janelia-kicad/LED-Display_G4_Hardware_Arena/docs/assets/arena_12-12_v2_back_iso-render.png

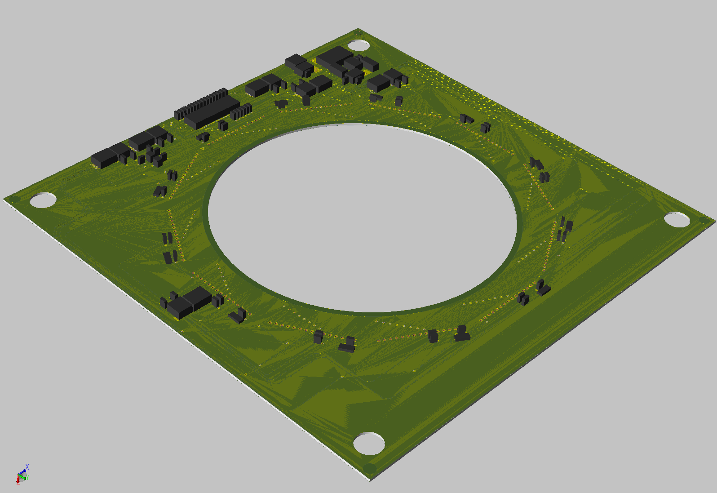
docs/assets/arena_12-12_v2_back_iso-render.png
