janelia-kicad/LED-Display_G4_Hardware_Arena/docs/assets/arena_12-12_v6p0_front_iso-render.png

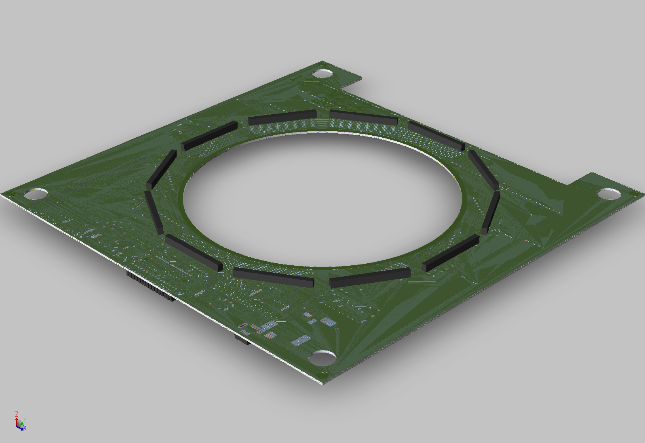
docs/assets/arena_12-12_v6p0_front_iso-render.png
