janelia-kicad/LED-Display_G4_Hardware_Arena/docs/assets/g4_with-placeholder_iso-photo.jpg

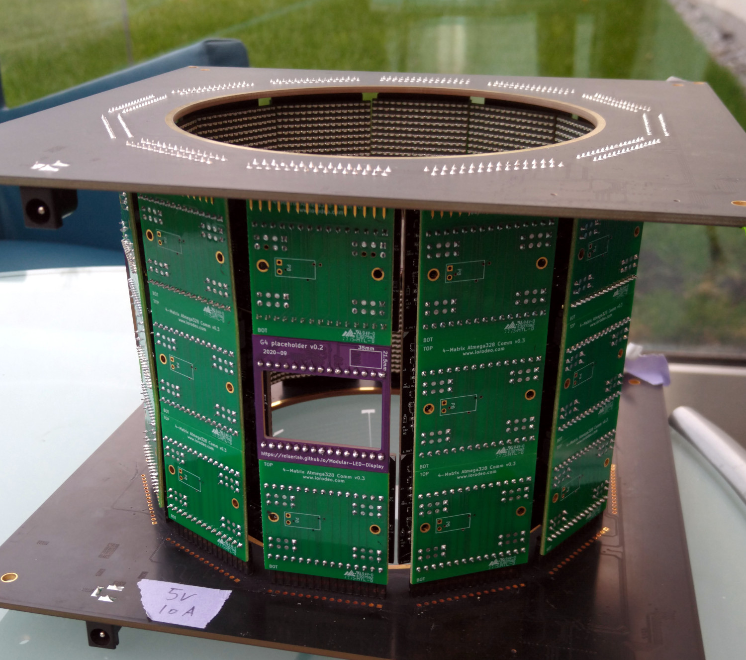
docs/assets/g4_with-placeholder_iso-photo.jpg
