janelia-kicad/LED-Display_G4_Hardware_Arena/docs/assets/g4_with-placeholder_photo.jpg

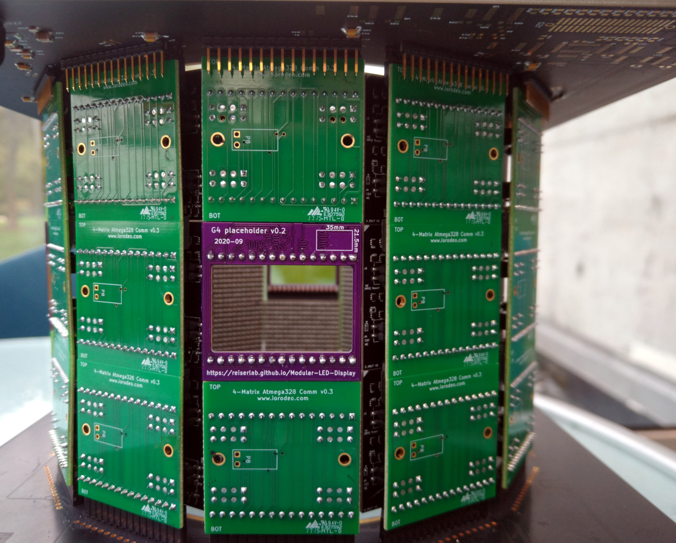
docs/assets/g4_with-placeholder_photo.jpg
