janelia-kicad/LED-Display_G4_Hardware_Arena/docs/assets/interconnect_v1_front_photo.jpg

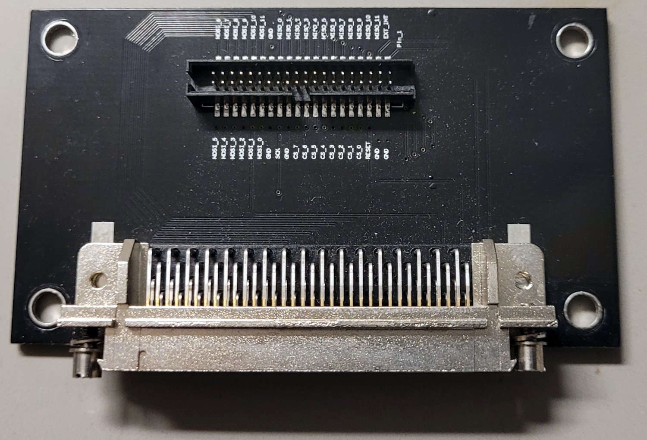
docs/assets/interconnect_v1_front_photo.jpg
