janelia-kicad/LED-Display_G4_Hardware_Arena/development/arena_12-12_w_vreg/ni/ni_arena_12-12_v0p1/production/version_0p1_r1/nonlscs_bom_ni_12-12_v0p1_r1.xlsx

Global parts for JLPCB assembly
Comment | Designator | Footprint | Qty | Digikey PN
DC Power Barrel Jack | J1 | through hole | 1 | CP-063AH-ND
15x1 female header, 0.1in pitch | P1,P2,P3,P4,P5,P6,P7,P8,P9,P10,P11,P12 | through hole | 12 | S7048-ND
Slide Switch SPDT | SW1 | through hole | 1 | CKC5102-ND
TE/NI 68 Position Connector, Vertical | J2 | through hole | 1 | A123166-ND
