janelia-kicad/LED-Display_G4_Hardware_Arena/development/arena_12-12/ni/ni_arena_12-12_v0p1/production/version_0p1_r1/BOM_JLCPCB_teensy_arena_12-12_v0p1_r1.xlsx

Comment | Designator | Footprint | LCSC Part #（optional） | Qty
0.1uF ceramic Capacitor | C1,C2,C3,C4,C5,C6,C7,C8,C9,C10 | 0603 | C1591 | 10
10uF Electrolytic Capacitor | C11,C13,C15,C17,C19,C21,C23,C25,C27,C29,C31,C33 | SMD,D4xL5.4mm | C2992602 | 12
22uF Electrolytic Capacitor | C12,C14,C16,C18,C20,C22,C24,C26,C28,C30,C32,C34 | SMD,D4xL5.4mm | C2895280 | 12
4-Pin Connector, JST SM04B-SRSS-TB or similar | J2 ,J3 | SMD,P=1mm | C145956 | 2
MOSFET N-channel | Q2 | SOT-23 | C165220 | 1
200 Ohm resistor | R1 | 0805 | C17540 | 1
20k Ohms resistor | R2 | 0805 | C4328 | 1
300 Ohm resistor | R3,R4,R5,R6,R7,R8,R9,R10,R11,R12,R13,R14 | 1206 | C17887 | 12
Level shifter TXB0108PWR | U1,U2,U3,U4,U5 | TSSOP-20 | C53406 | 5
Linear Voltage Regulators (LDO) 5V | U6,U7,U8,U9,U10,U11,U12,U13,U14,U15,U16,U17 | TO-252 | C2980701 | 12
DC Power Barrel Jack | J1 | through hole | global parts | 1
15x1 female header, 0.1in pitch | P1,P2,P3,P4,P5,P6,P7,P8,P9,P10,P11,P12 | through hole | global parts | 12
Slide Switch SPDT | SW1 | through hole | global parts | 1
