janelia-kicad/LED-Display_G4_Hardware_Arena/development/arena_flat_6/teensy4p1/arena_flat_6_tn_v0p1/arena_pdfs/arena.pdf

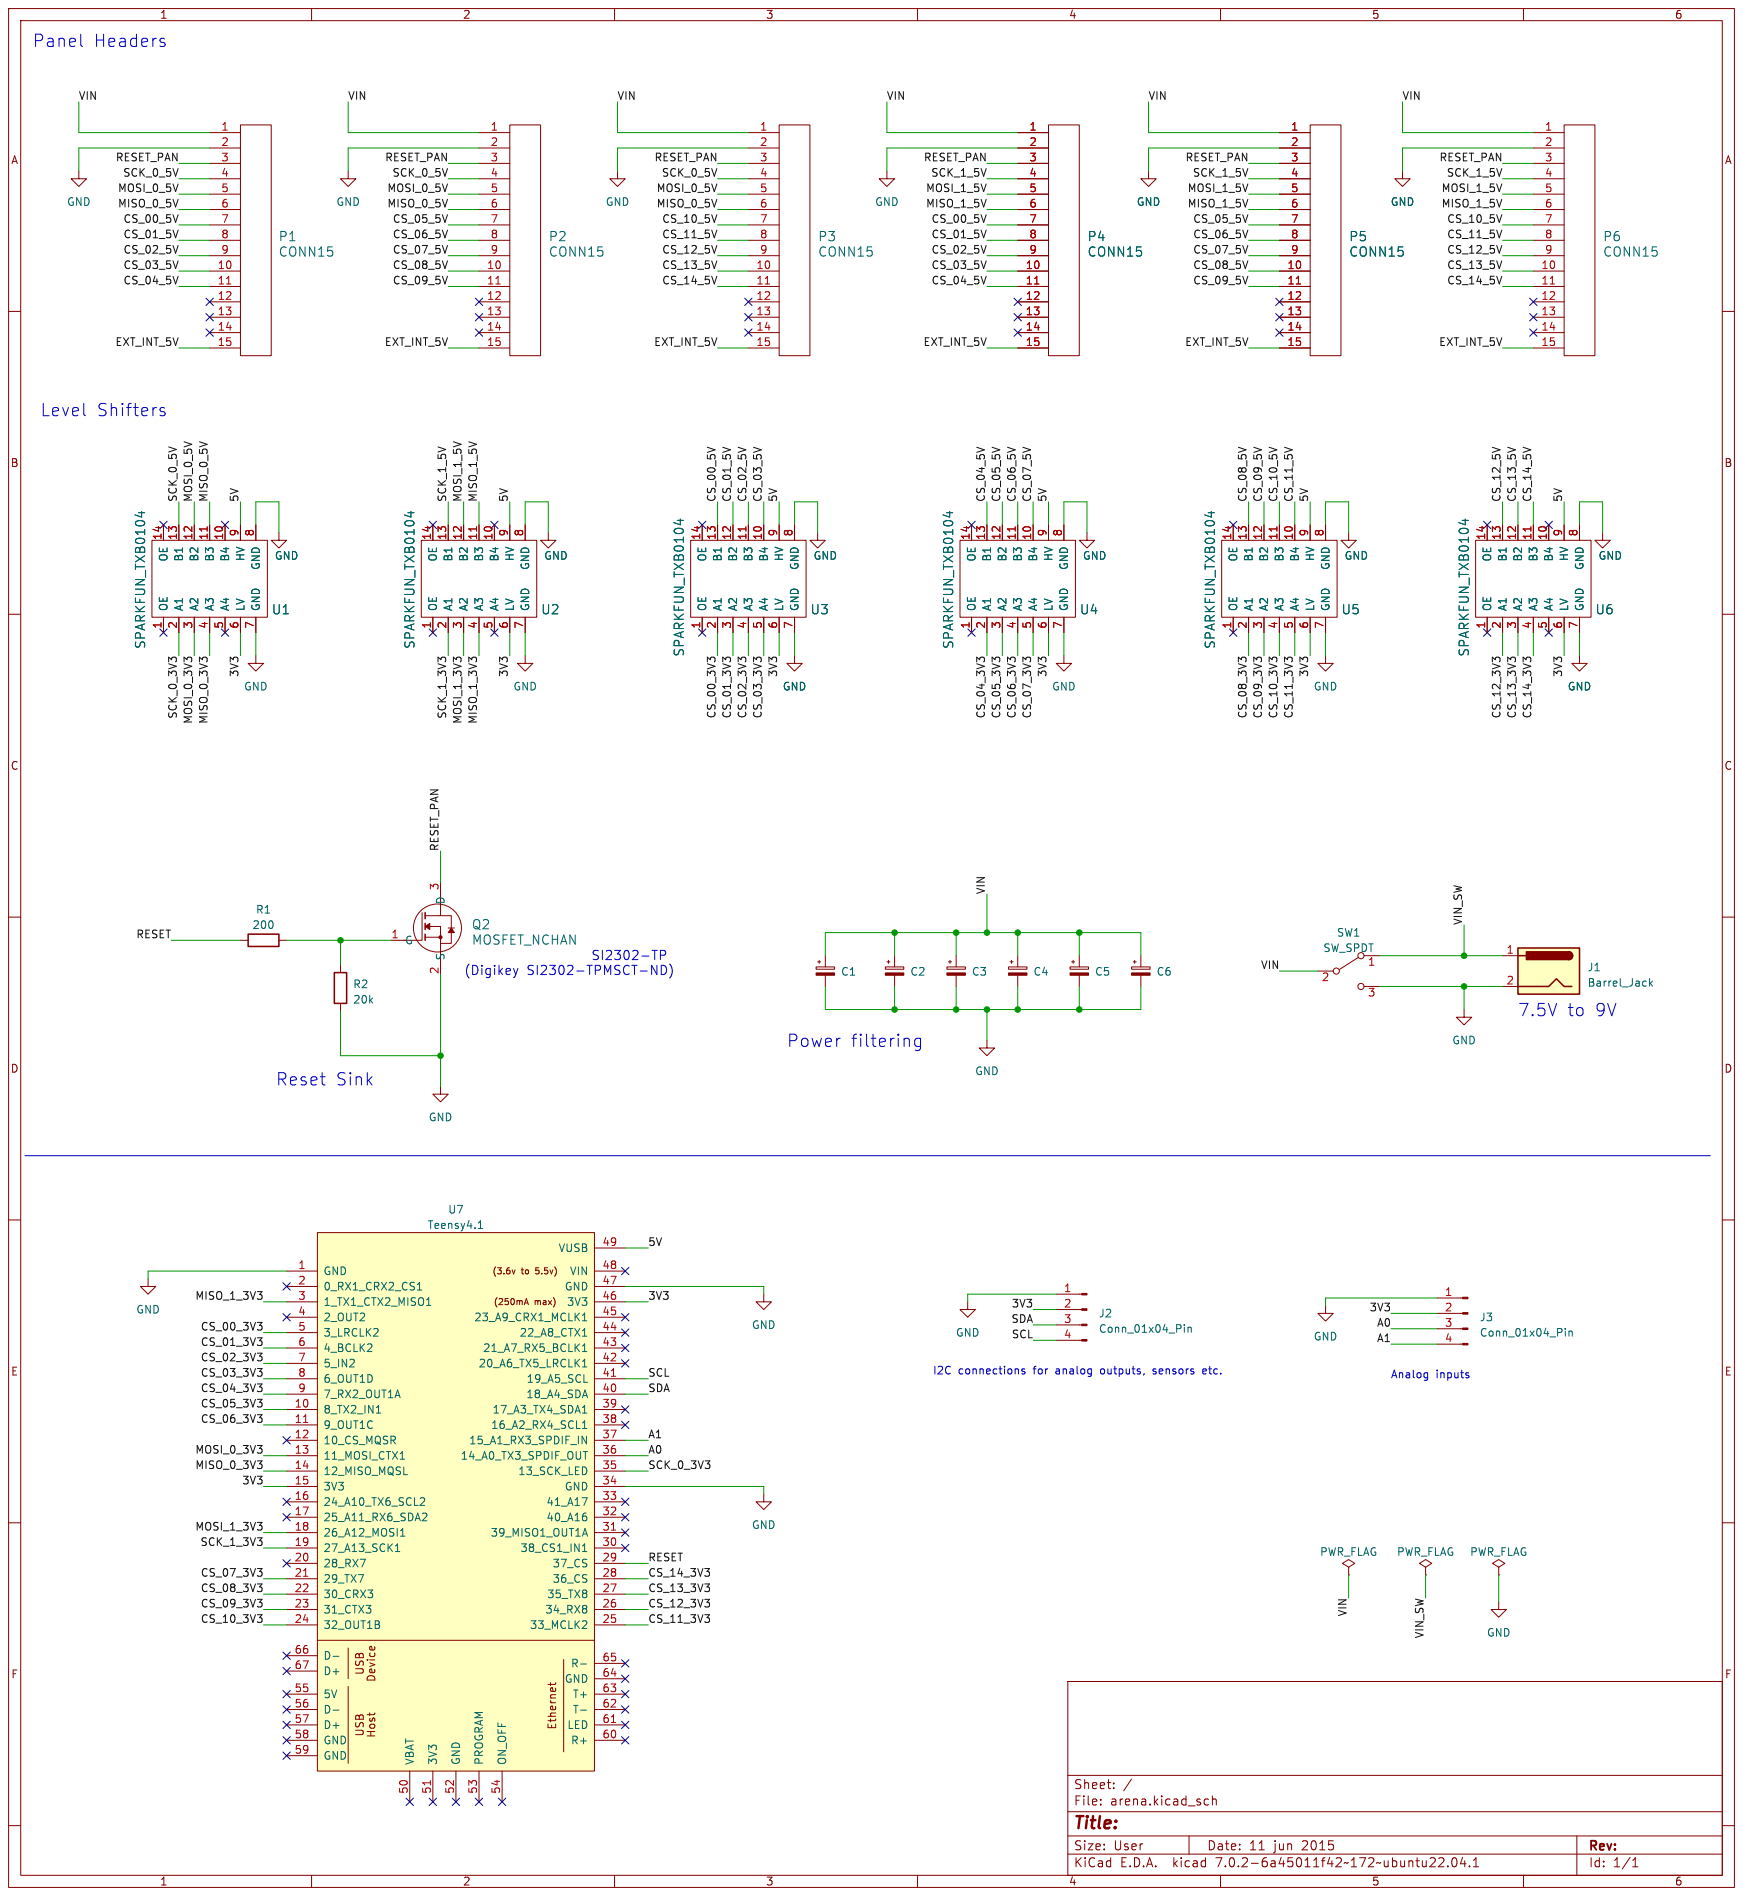
[picture p38: page 1]

9 GND GND GND U1 SPARKFUN_TXB0104 OE

Id: 1/1 Title: File: arena.kicad_sch Sheet: /
