janelia-kicad/LED-Display_G4_Hardware_Arena/docs/assets/arena_12-12_v5_schematic.pdf

5

4

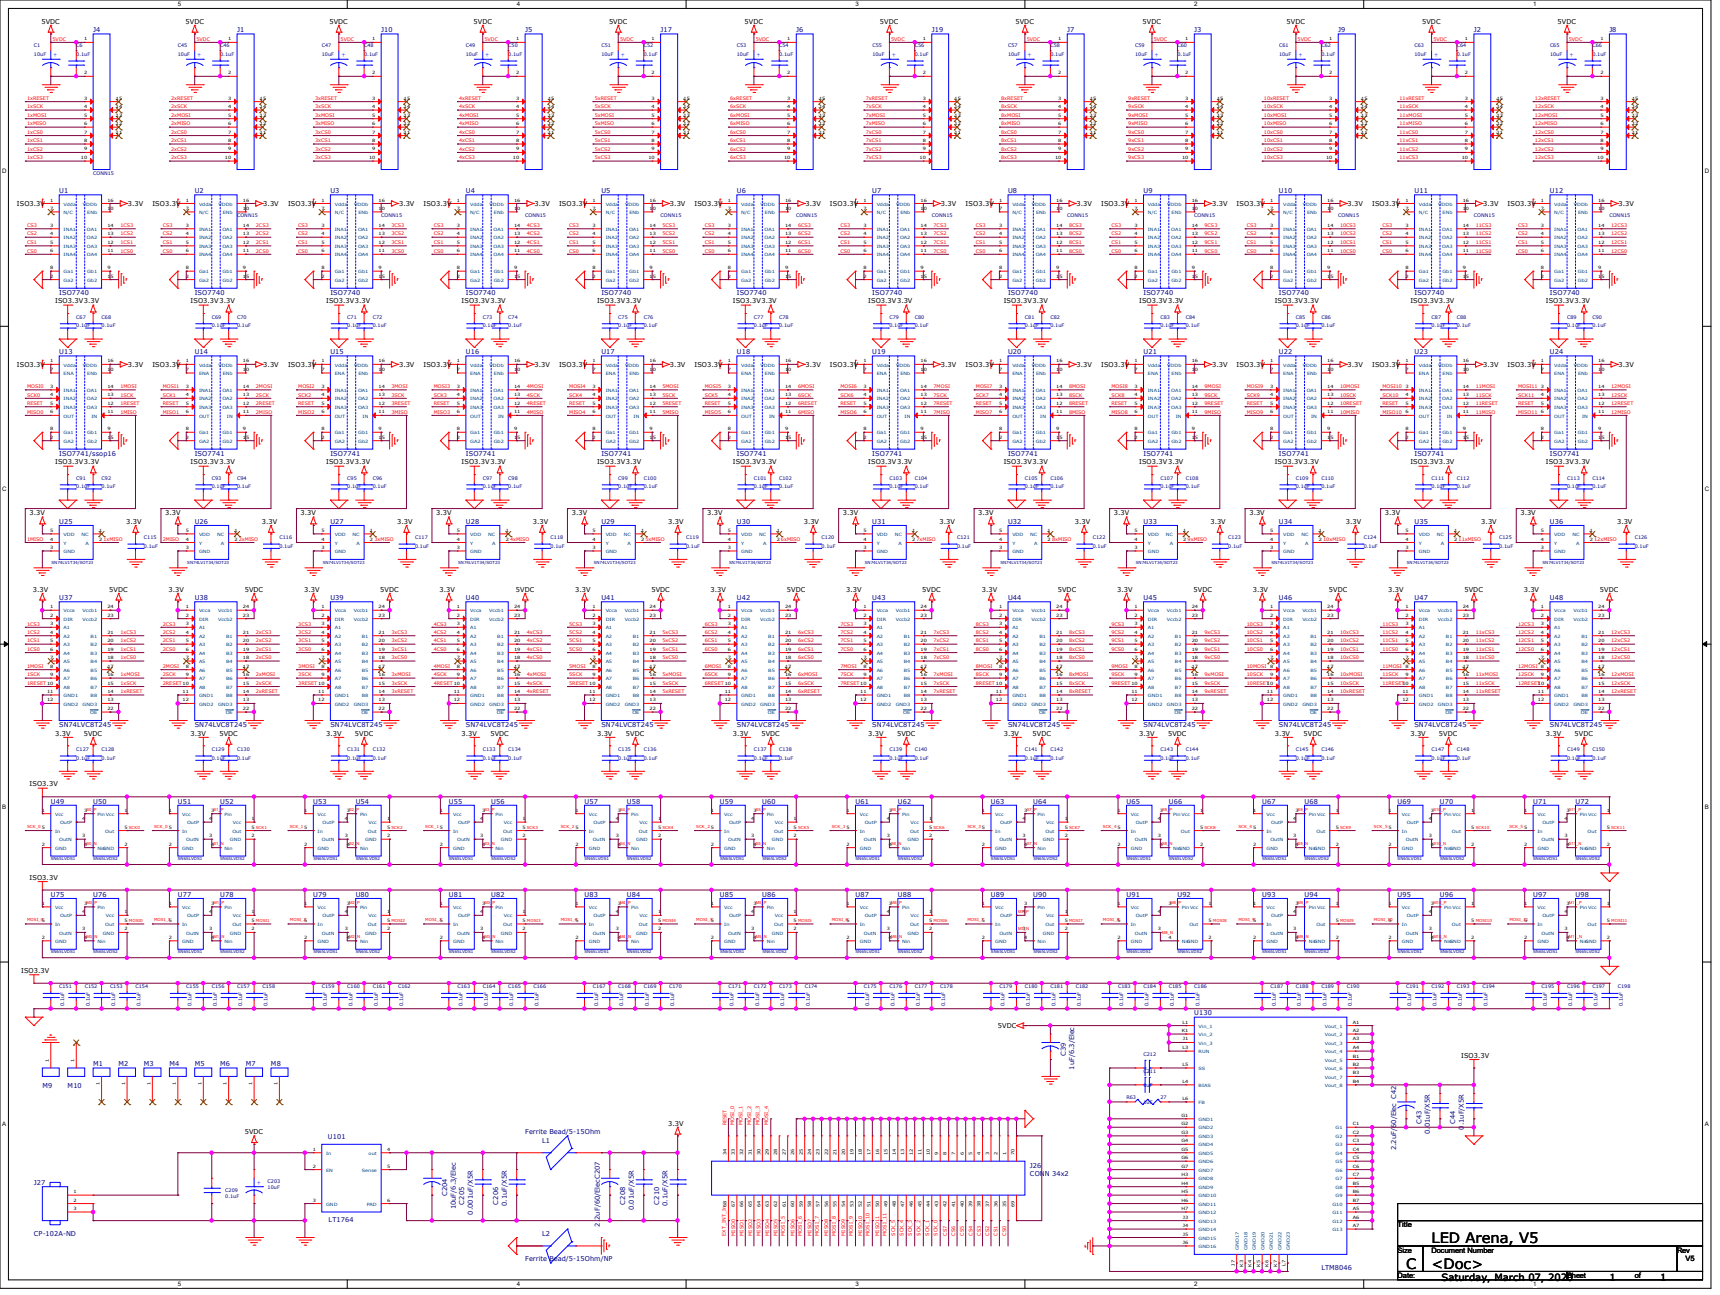
[picture p40: page 1]
