janelia-kicad/LED-Display_G4_Hardware_Arena/legacy/arena_12-12/production_v5/arena_12-12_v5_assembly.pdf

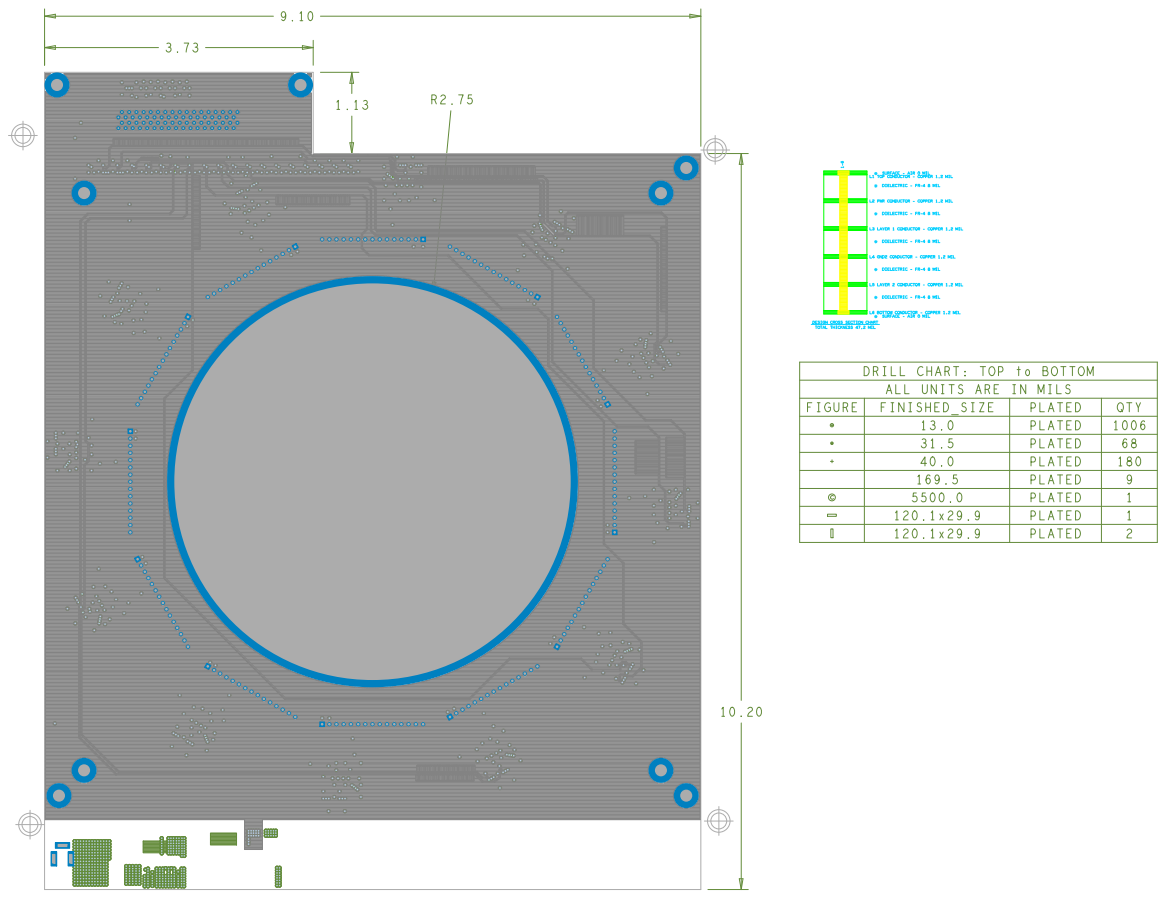
[picture p41: page 1]
